Minorzar/2223_Projet1A_SNES_Controller/Project_controller/Hardware/# Flowchart/SNES_Architecture.png

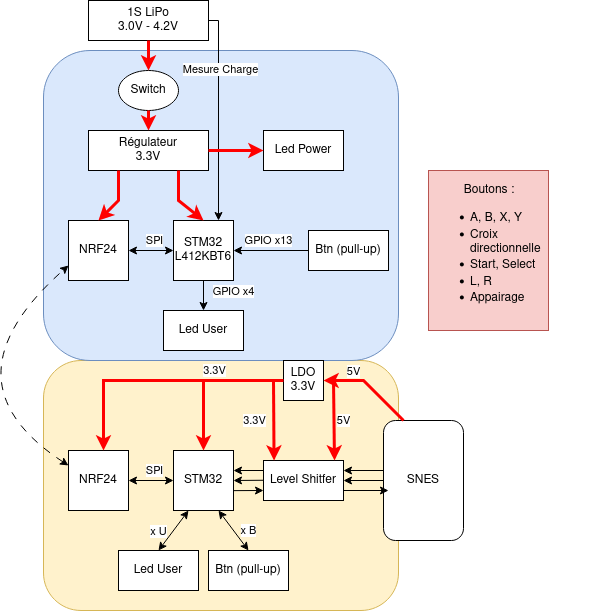
Project_controller/Hardware/# Flowchart/SNES_Architecture.png
