Minorzar/2223_Projet1A_SNES_Controller/Project_controller/Hardware/Kicad/# Image/Routing_V2_1/Plug_NRF24L01_Exclude_V2_1_PCB.png

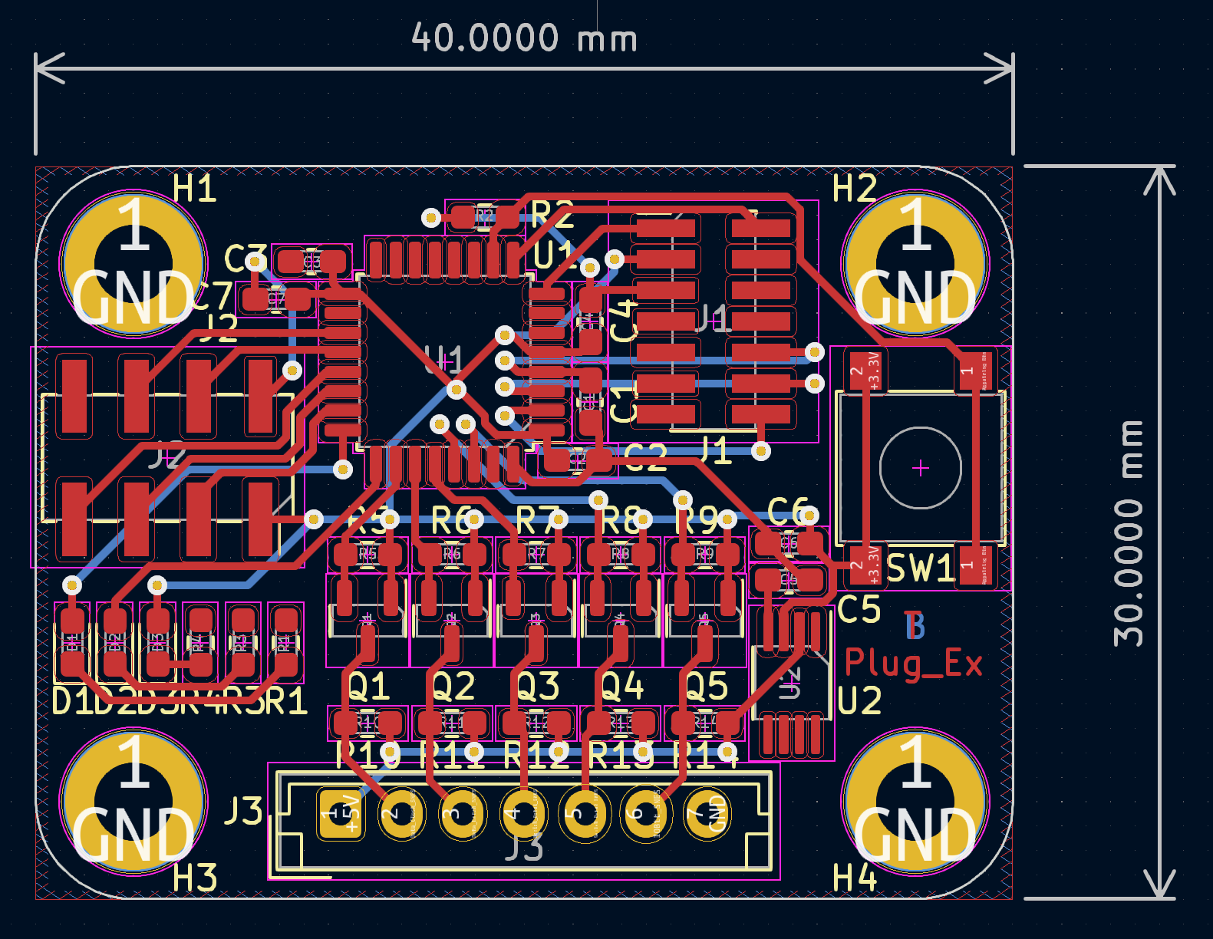
Project_controller/Hardware/Kicad/# Image/Routing_V2_1/Plug_NRF24L01_Exclude_V2_1_PCB.png
