Minorzar/2223_Projet1A_SNES_Controller/Project_controller/Hardware/Kicad/# Image/Routing_V4_0_a/Plug_NRF24L01_Exclude_V4_0_a-2_PCB.png

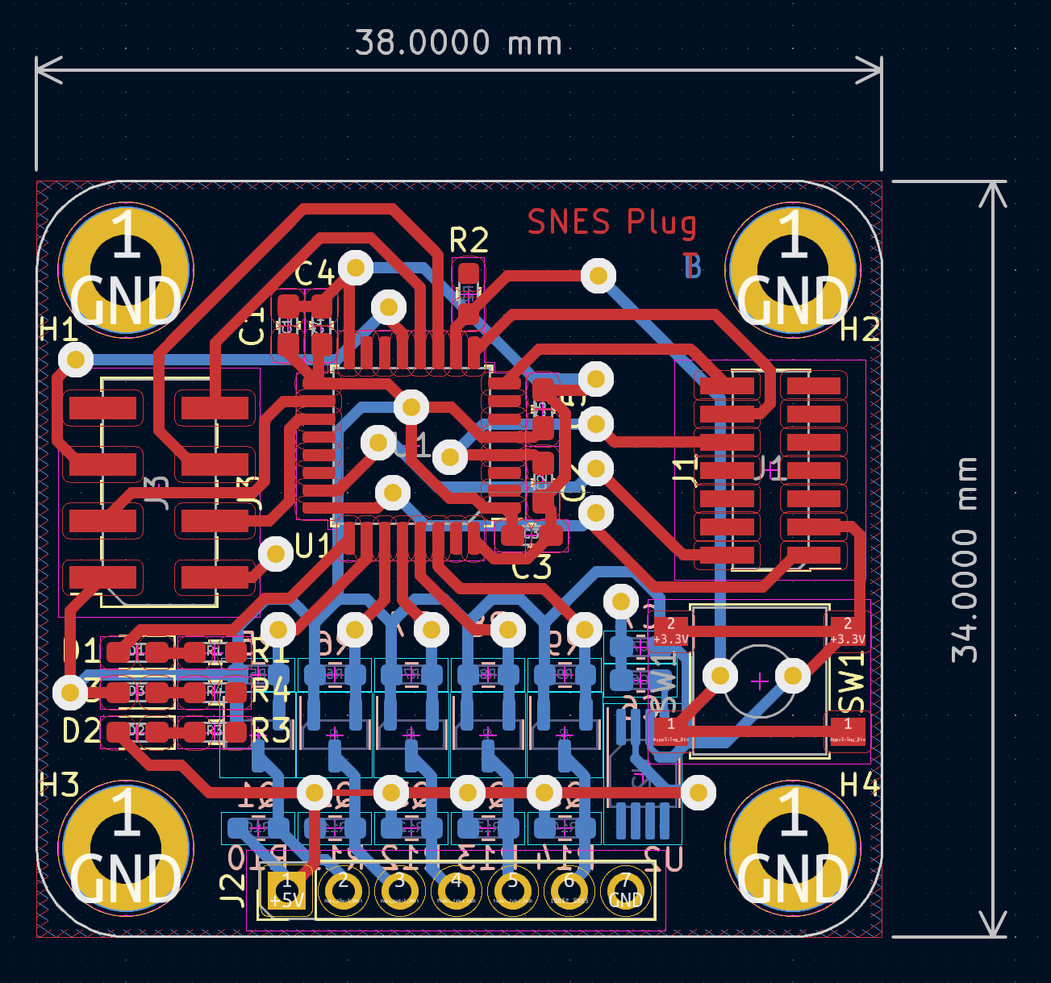
Project_controller/Hardware/Kicad/# Image/Routing_V4_0_a/Plug_NRF24L01_Exclude_V4_0_a-2_PCB.png
