Minorzar/2223_Projet1A_SNES_Controller/Project_controller/Hardware/Shell/Controller_Shell/B.PNG

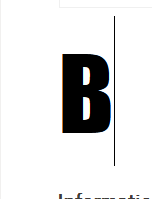
Project_controller/Hardware/Shell/Controller_Shell/B.PNG
