Minorzar/2223_Projet1A_SNES_Controller/Project_controller/Software/# Flowchart/Flowchart_Controller.jpg

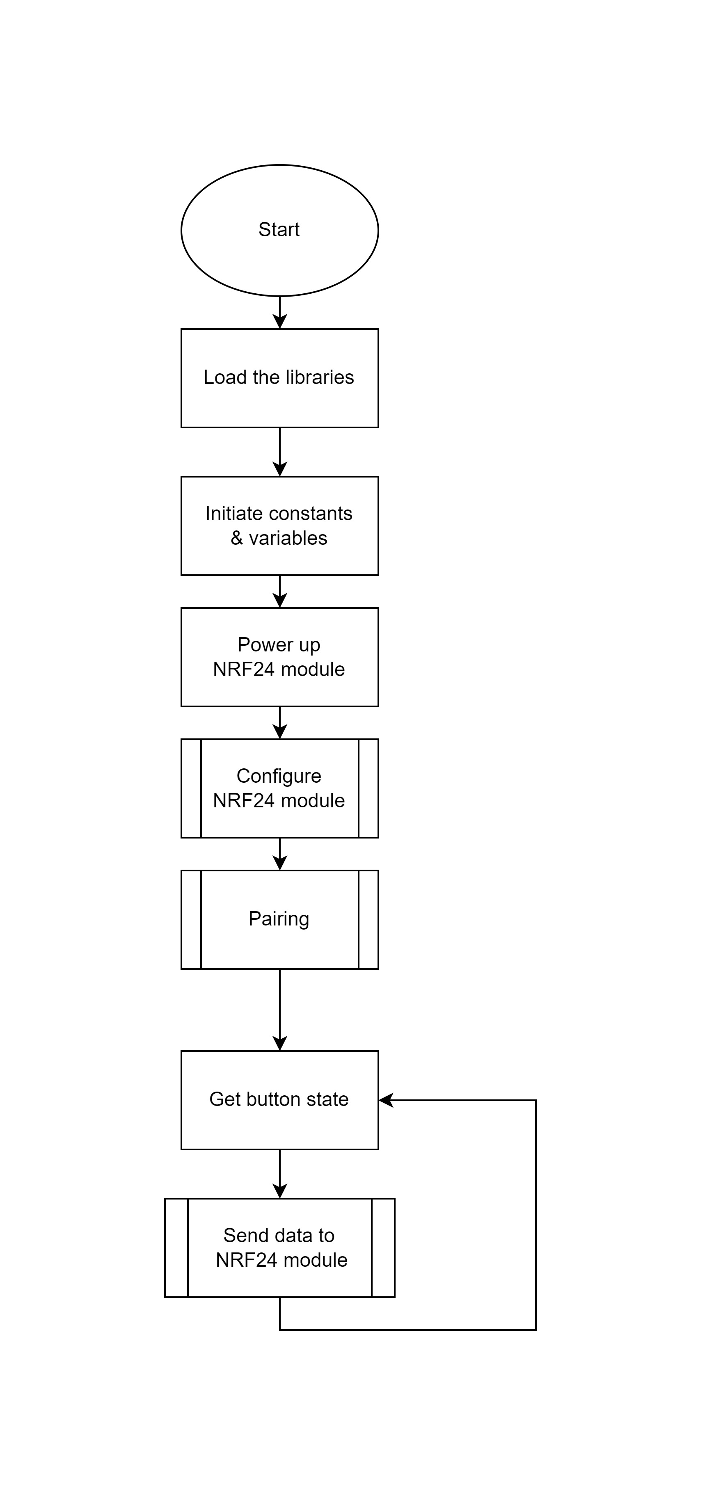
Project_controller/Software/# Flowchart/Flowchart_Controller.jpg
