Minorzar/2223_Projet1A_SNES_Controller/Project_controller/Hardware/Shell/Controller_Shell/V3/cache v3.stl

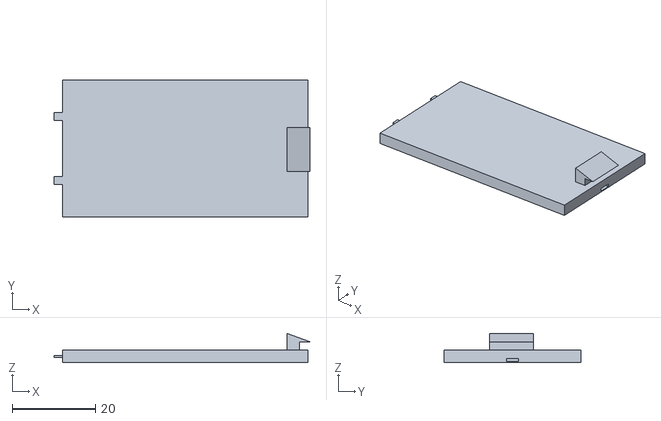
[picture p33: CAD file, 2023-05-16]
Project_controller/Hardware/Shell/Controller_Shell/V3/cache v3.stl
61.5 x 33.0 x 7.00
