Minorzar/2223_Projet1A_SNES_Controller/Project_controller/Hardware/Shell/Controller_Shell/orignal/button start select.stl

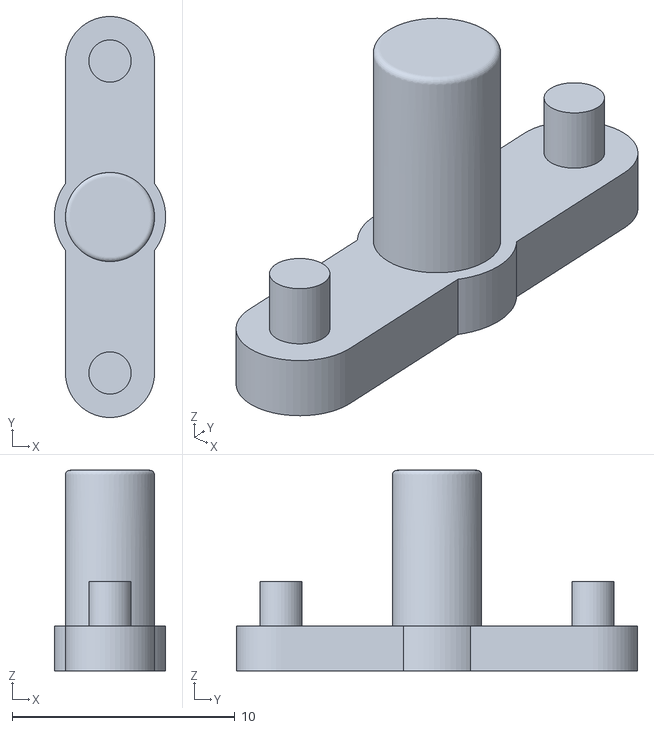
[picture p34: CAD file, 2023-05-11]
Project_controller/Hardware/Shell/Controller_Shell/orignal/button start select.stl
4.99 x 18.0 x 9.00
