Minorzar/2223_Projet1A_SNES_Controller/Project_controller/Hardware/Shell/Controller_Shell/orignal/Button connection.stl

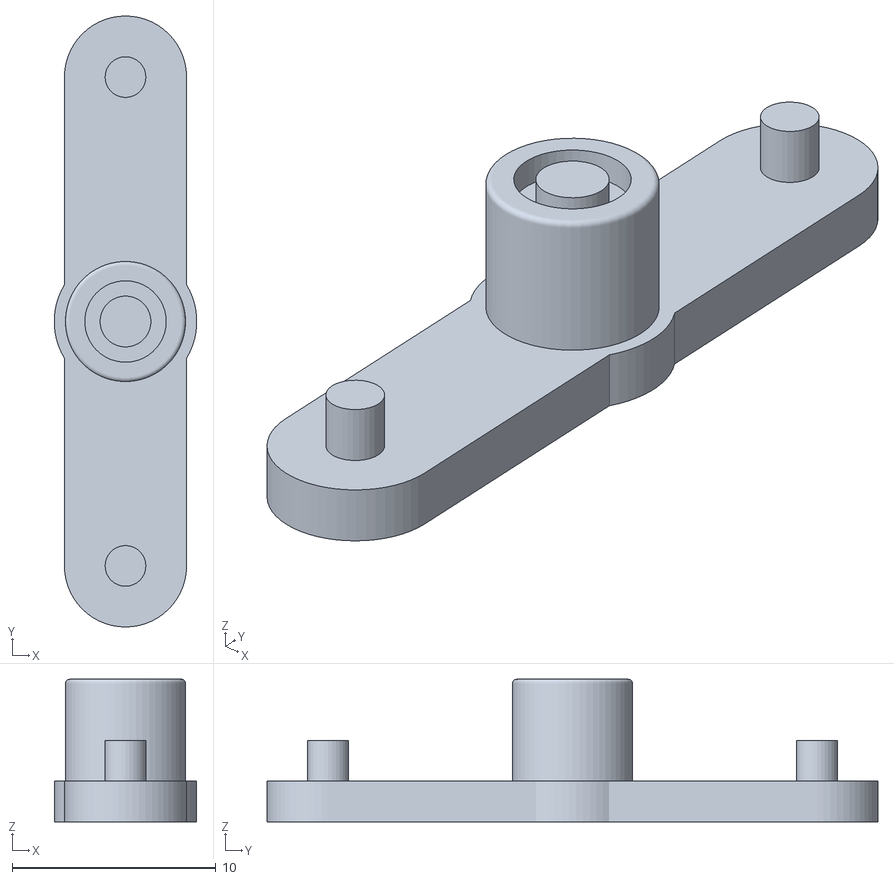
[picture p35: CAD file, 2023-05-10]
Project_controller/Hardware/Shell/Controller_Shell/orignal/Button connection.stl
6.99 x 30.0 x 7.00
