Minorzar/2223_Projet1A_SNES_Controller/Project_controller/Hardware/Shell/Controller_Shell/V3/Button connection v2.stl

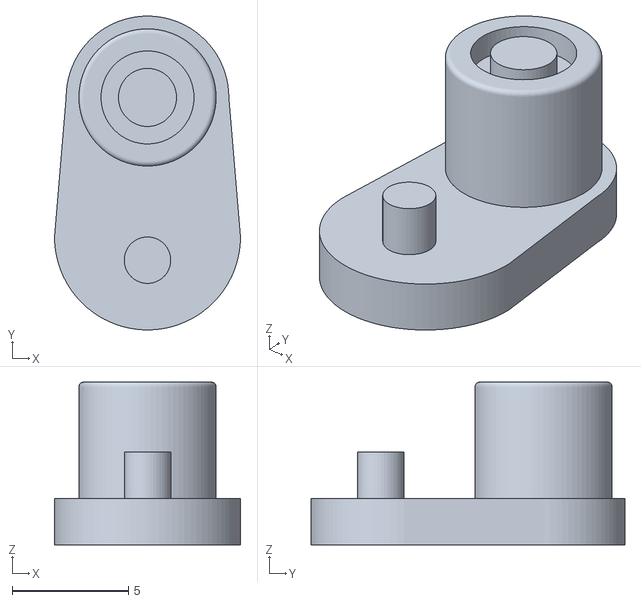
[picture p36: CAD file, 2023-05-16]
Project_controller/Hardware/Shell/Controller_Shell/V3/Button connection v2.stl
8.00 x 13.5 x 7.00
