Minorzar/2223_Projet1A_SNES_Controller/Project_controller/Hardware/Shell/Controller_Shell/V3/Button X v3.stl

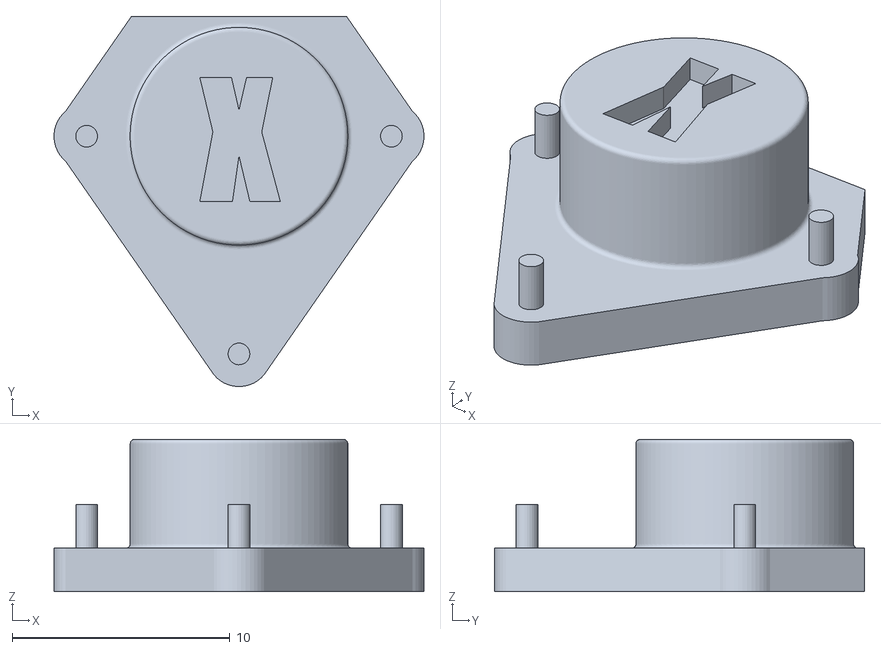
[picture p37: CAD file, 2023-05-16]
Project_controller/Hardware/Shell/Controller_Shell/V3/Button X v3.stl
17.0 x 17.0 x 7.00
