Minorzar/2223_Projet1A_SNES_Controller/Hardware/Kicad/NRF24L01_Include/SNES_Controller_NRF24L01_Include.kicad_pcb

## KiCad design Hardware/Kicad/NRF24L01_Include/SNES_Controller_NRF24L01_Include.kicad_pcb (2023-04-16)

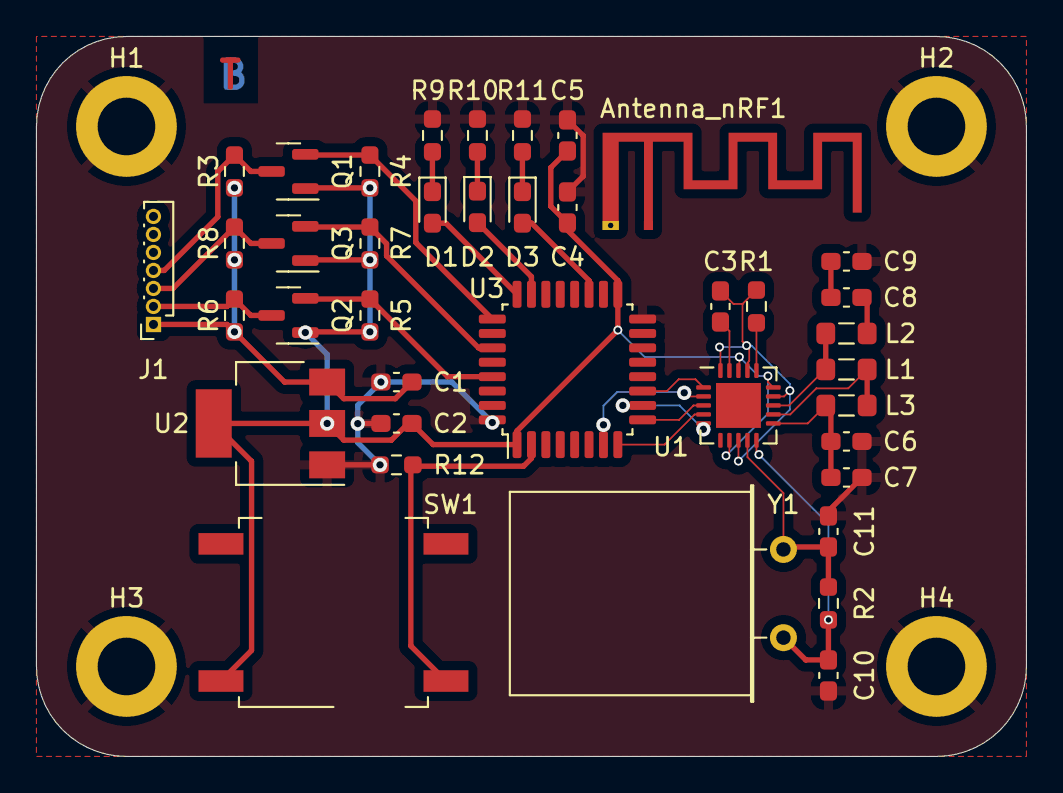
[picture p50: board SNES_Controller_NRF24L01_Include.kicad_pcb from above]

Board: 2 copper layers, 55.0 x 40.0 mm, 43 parts (0 on the bottom side), 31 nets.

Parts:
Antenna_nRF1: Texas_SWRA117D_2.4GHz_Right
C1, C2: 1u; C_0603_1608Metric_Pad1.08x0.95mm_HandSolder
C3: 33n; C_0603_1608Metric_Pad1.08x0.95mm_HandSolder
C4: 10n; C_0603_1608Metric_Pad1.08x0.95mm_HandSolder
C5: 1n; C_0603_1608Metric_Pad1.08x0.95mm_HandSolder
C6: 2.2n; C_0603_1608Metric_Pad1.08x0.95mm_HandSolder
C7: 4.7p; C_0603_1608Metric_Pad1.08x0.95mm_HandSolder
C8: 1.5p; C_0603_1608Metric_Pad1.08x0.95mm_HandSolder
C9: 1.0p; C_0603_1608Metric_Pad1.08x0.95mm_HandSolder
C10, C11: 22p; C_0603_1608Metric_Pad1.08x0.95mm_HandSolder
D1, D2, D3: LED_Small; D_0603_1608Metric_Pad1.05x0.95mm_HandSolder
H1, H2, H3, H4: MountingHole_Pad; MountingHole_3.2mm_M3_DIN965_Pad
J1: Conn_01x07_Socket; PinSocket_1x07_P1.00mm_Vertical
L1: 8.2n; L_0805_2012Metric_Pad1.05x1.20mm_HandSolder
L2: 3.9n; L_0805_2012Metric_Pad1.05x1.20mm_HandSolder
L3: 2.7n; L_0805_2012Metric_Pad1.05x1.20mm_HandSolder
Q1, Q2, Q3: 2N7002; SOT-23
R1: 22k; R_0603_1608Metric_Pad0.98x0.95mm_HandSolder
R2: 1M; R_0603_1608Metric_Pad0.98x0.95mm_HandSolder
R3, R4, R5, R6, R7, R8, R12: 10k; R_0603_1608Metric_Pad0.98x0.95mm_HandSolder
R9, R10, R11: 1k; R_0603_1608Metric_Pad0.98x0.95mm_HandSolder
SW1: SW_Push; SW_MEC_5GSH9
U1: NRF24L01; QFN-20-1EP_4x4mm_P0.5mm_EP2.5x2.5mm
U2: AMS1117-3.3; SOT-223-3_TabPin2
U3: STM32L412KBTx; LQFP-32_7x7mm_P0.8mm
Y1: 16 MHz; Crystal_HC49-U_Horizontal

Connections:
+5V: C1.1, J1.1, R3.1, R6.1, R8.1, U2.3 (VI)
ANT1: L1.2, L3.1, U1.12 (ANT1)
ANT2: L1.1, L2.1, U1.13 (ANT2)
Appairing_Btn: R12.1, SW1.2, U3.2 (PC14)
Chip_Enable: U1.1 (CE), U3.11 (PA5)
Data_Clock_SNES: J1.2, Q2.3 (D), R6.2
Data_Clock_STM32: Q2.2 (S), R5.2, U3.29 (PB6)
Data_Latch_SNES: J1.3, Q3.3 (D), R8.2
Data_Latch_STM32: Q3.2 (S), R7.2, U3.27 (PB4)
GND: C1.2, C2.2, C4.2, C5.2, C6.2, C7.2, C9.1, C10.2, C11.2, H1.1, H2.1, H3.1, H4.1, R9.2, R10.2, R11.2, R12.2, U2.1 (GND), U3.16 (VSS), U3.32 (VSS)
GND1: C3.2, R1.2, U1.8 (VSS), U1.14 (VSS), U1.17 (VSS), U1.20 (VSS)
unnamed: C8.2, L2.2
unnamed: D1.1 (K), R9.1
unnamed: D2.1 (K), R10.1
unnamed: D3.1 (K), R11.1
unnamed: C3.1, U1.19 (DVDD)
unnamed: R1.1, U1.16 (IREF)
Player1_LED: D1.2 (A), U3.24 (PA14)
Player2_LED: D2.2 (A), U3.23 (PA13)
RF_Output: Antenna_nRF1.1 (Feed_point), C8.1, C9.2
SPI_Chip_Select: U1.2 (CSN), U3.7 (PA1)
SPI_Clock: U1.3 (SCK), U3.9 (PA3)
SPI_Digital_Input: U1.4 (MOSI), U3.8 (PA2)
SPI_Digital_Output: U1.5 (MISO), U3.10 (PA4)
Serial_Data_SNES: J1.4, Q1.3 (D), R3.2
Serial_Data_STM32: Q1.2 (S), R4.2, U3.25 (PA15)
Status_LED: D3.2 (A), U3.19 (PA9)
VDD_NRF: C2.1, C4.1, C5.1, Q1.1 (G), Q2.1 (G), Q3.1 (G), R4.1, R5.1, R7.1, SW1.1, U1.7 (VDD), U1.15 (VDD), U1.18 (VDD), U2.2 (VO), U3.1 (VDD), U3.17 (VDD)
VDD_PA: C6.1, C7.1, L3.2, U1.11 (VDD_PA)
XC1: C10.1, R2.1, U1.10 (XC1), Y1.2
XC2: C11.1, R2.2, U1.9 (XC2), Y1.1
