Minorzar/2223_Projet1A_SNES_Controller/Project_controller/Software/Controller/NUCLEO-H7A3_NRF24_v2/Core/Src/usart.c

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
/* Includes ------------------------------------------------------------------*/
#include "usart.h"

/* USER CODE BEGIN 0 */
#include <string.h>

uint8_t uartFlag;
char uartTxBuffer[UARTTXBUFFERSIZE];
char uartRxBuffer[UARTRXBUFFERSIZE];
/* USER CODE END 0 */

UART_HandleTypeDef huart3;

/* USART3 init function */

void MX_USART3_UART_Init(void)
{

  huart3.Instance = USART3;
  huart3.Init.BaudRate = 115200;
  huart3.Init.WordLength = UART_WORDLENGTH_8B;
  huart3.Init.StopBits = UART_STOPBITS_1;
  huart3.Init.Parity = UART_PARITY_NONE;
  huart3.Init.Mode = UART_MODE_TX_RX;
  huart3.Init.HwFlowCtl = UART_HWCONTROL_NONE;
  huart3.Init.OverSampling = UART_OVERSAMPLING_16;
  huart3.Init.OneBitSampling = UART_ONE_BIT_SAMPLE_DISABLE;
  huart3.Init.ClockPrescaler = UART_PRESCALER_DIV1;
  huart3.AdvancedInit.AdvFeatureInit = UART_ADVFEATURE_NO_INIT;
  if (HAL_UART_Init(&huart3) != HAL_OK)
  {
    Error_Handler();
  }
  if (HAL_UARTEx_SetTxFifoThreshold(&huart3, UART_TXFIFO_THRESHOLD_1_8) != HAL_OK)
  {
    Error_Handler();
  }
  if (HAL_UARTEx_SetRxFifoThreshold(&huart3, UART_RXFIFO_THRESHOLD_1_8) != HAL_OK)
  {
    Error_Handler();
  }
  if (HAL_UARTEx_DisableFifoMode(&huart3) != HAL_OK)
  {
    Error_Handler();
  }
  /* USER CODE BEGIN USART3_Init 2 */
  HAL_UART_Receive_IT(&huart3, (uint8_t*) uartRxBuffer, 1);
  /* USER CODE END USART3_Init 2 */

}

void HAL_UART_MspInit(UART_HandleTypeDef* uartHandle)
{

  GPIO_InitTypeDef GPIO_InitStruct = {0};
  RCC_PeriphCLKInitTypeDef PeriphClkInitStruct = {0};
  if(uartHandle->Instance==USART3)
  {
  /** Initializes the peripherals clock
  */
    PeriphClkInitStruct.PeriphClockSelection = RCC_PERIPHCLK_USART3;
    PeriphClkInitStruct.Usart234578ClockSelection = RCC_USART234578CLKSOURCE_D2PCLK1;
    if (HAL_RCCEx_PeriphCLKConfig(&PeriphClkInitStruct) != HAL_OK)
    {
      Error_Handler();
    }

    /* USART3 clock enable */
    __HAL_RCC_USART3_CLK_ENABLE();

    __HAL_RCC_GPIOD_CLK_ENABLE();
    /**USART3 GPIO Configuration
    PD8     ------> USART3_TX
    PD9     ------> USART3_RX
    */
    GPIO_InitStruct.Pin = STLINK_RX_Pin|STLINK_TX_Pin;
    GPIO_InitStruct.Mode = GPIO_MODE_AF_PP;
    GPIO_InitStruct.Pull = GPIO_NOPULL;
    GPIO_InitStruct.Speed = GPIO_SPEED_FREQ_LOW;
    GPIO_InitStruct.Alternate = GPIO_AF7_USART3;
    HAL_GPIO_Init(GPIOD, &GPIO_InitStruct);

    /* USART3 interrupt Init */
    HAL_NVIC_SetPriority(USART3_IRQn, 0, 0);
    HAL_NVIC_EnableIRQ(USART3_IRQn);
  }
}

void HAL_UART_MspDeInit(UART_HandleTypeDef* uartHandle)
{

  if(uartHandle->Instance==USART3)
  {
    /* Peripheral clock disable */
    __HAL_RCC_USART3_CLK_DISABLE();

    /**USART3 GPIO Configuration
    PD8     ------> USART3_TX
    PD9     ------> USART3_RX
    */
    HAL_GPIO_DeInit(GPIOD, STLINK_RX_Pin|STLINK_TX_Pin);

    /* USART3 interrupt Deinit */
    HAL_NVIC_DisableIRQ(USART3_IRQn);
  }
}

/* USER CODE BEGIN 1 */
void HAL_UART_RxCpltCallback(UART_HandleTypeDef *huart)
{
	uartFlag = 1;
	uartTxBuffer[0]=uartRxBuffer[0];
	HAL_UART_Transmit(&huart3, (uint8_t*) uartTxBuffer, 1, 100);
	HAL_UART_Receive_IT(&huart3, (uint8_t*) uartRxBuffer, 1);

}

HAL_StatusTypeDef HAL_UART_Print(char* buffer){
	return HAL_UART_Transmit(&huart3, (uint8_t*)buffer, strlen(buffer), 100);
}

/* USER CODE END 1 */
